CIRCUITSTATE/PBSEQ-D1/Export/R0.1/[1] 12-05-2024/PCB/PBSEQ-D1-R0.1-F_Silkscreen.pdf

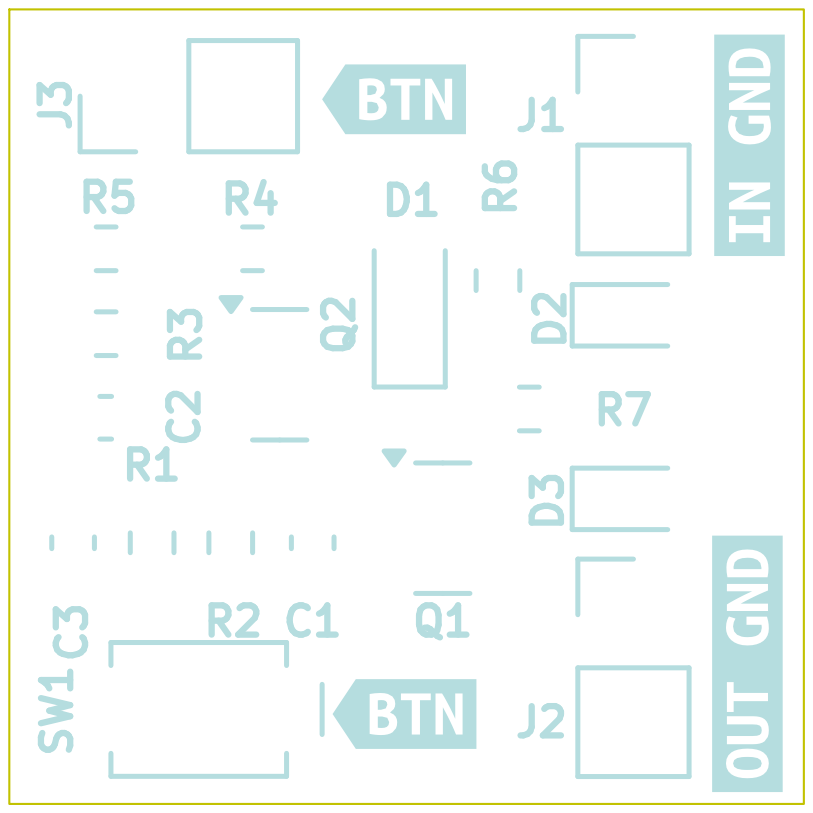
[picture p12: page 1]
