CIRCUITSTATE/PBSEQ-D1/Export/R0.1/[1] 12-05-2024/SCH/PBSEQ-D1-R0.1-SCH-12052024-1.pdf

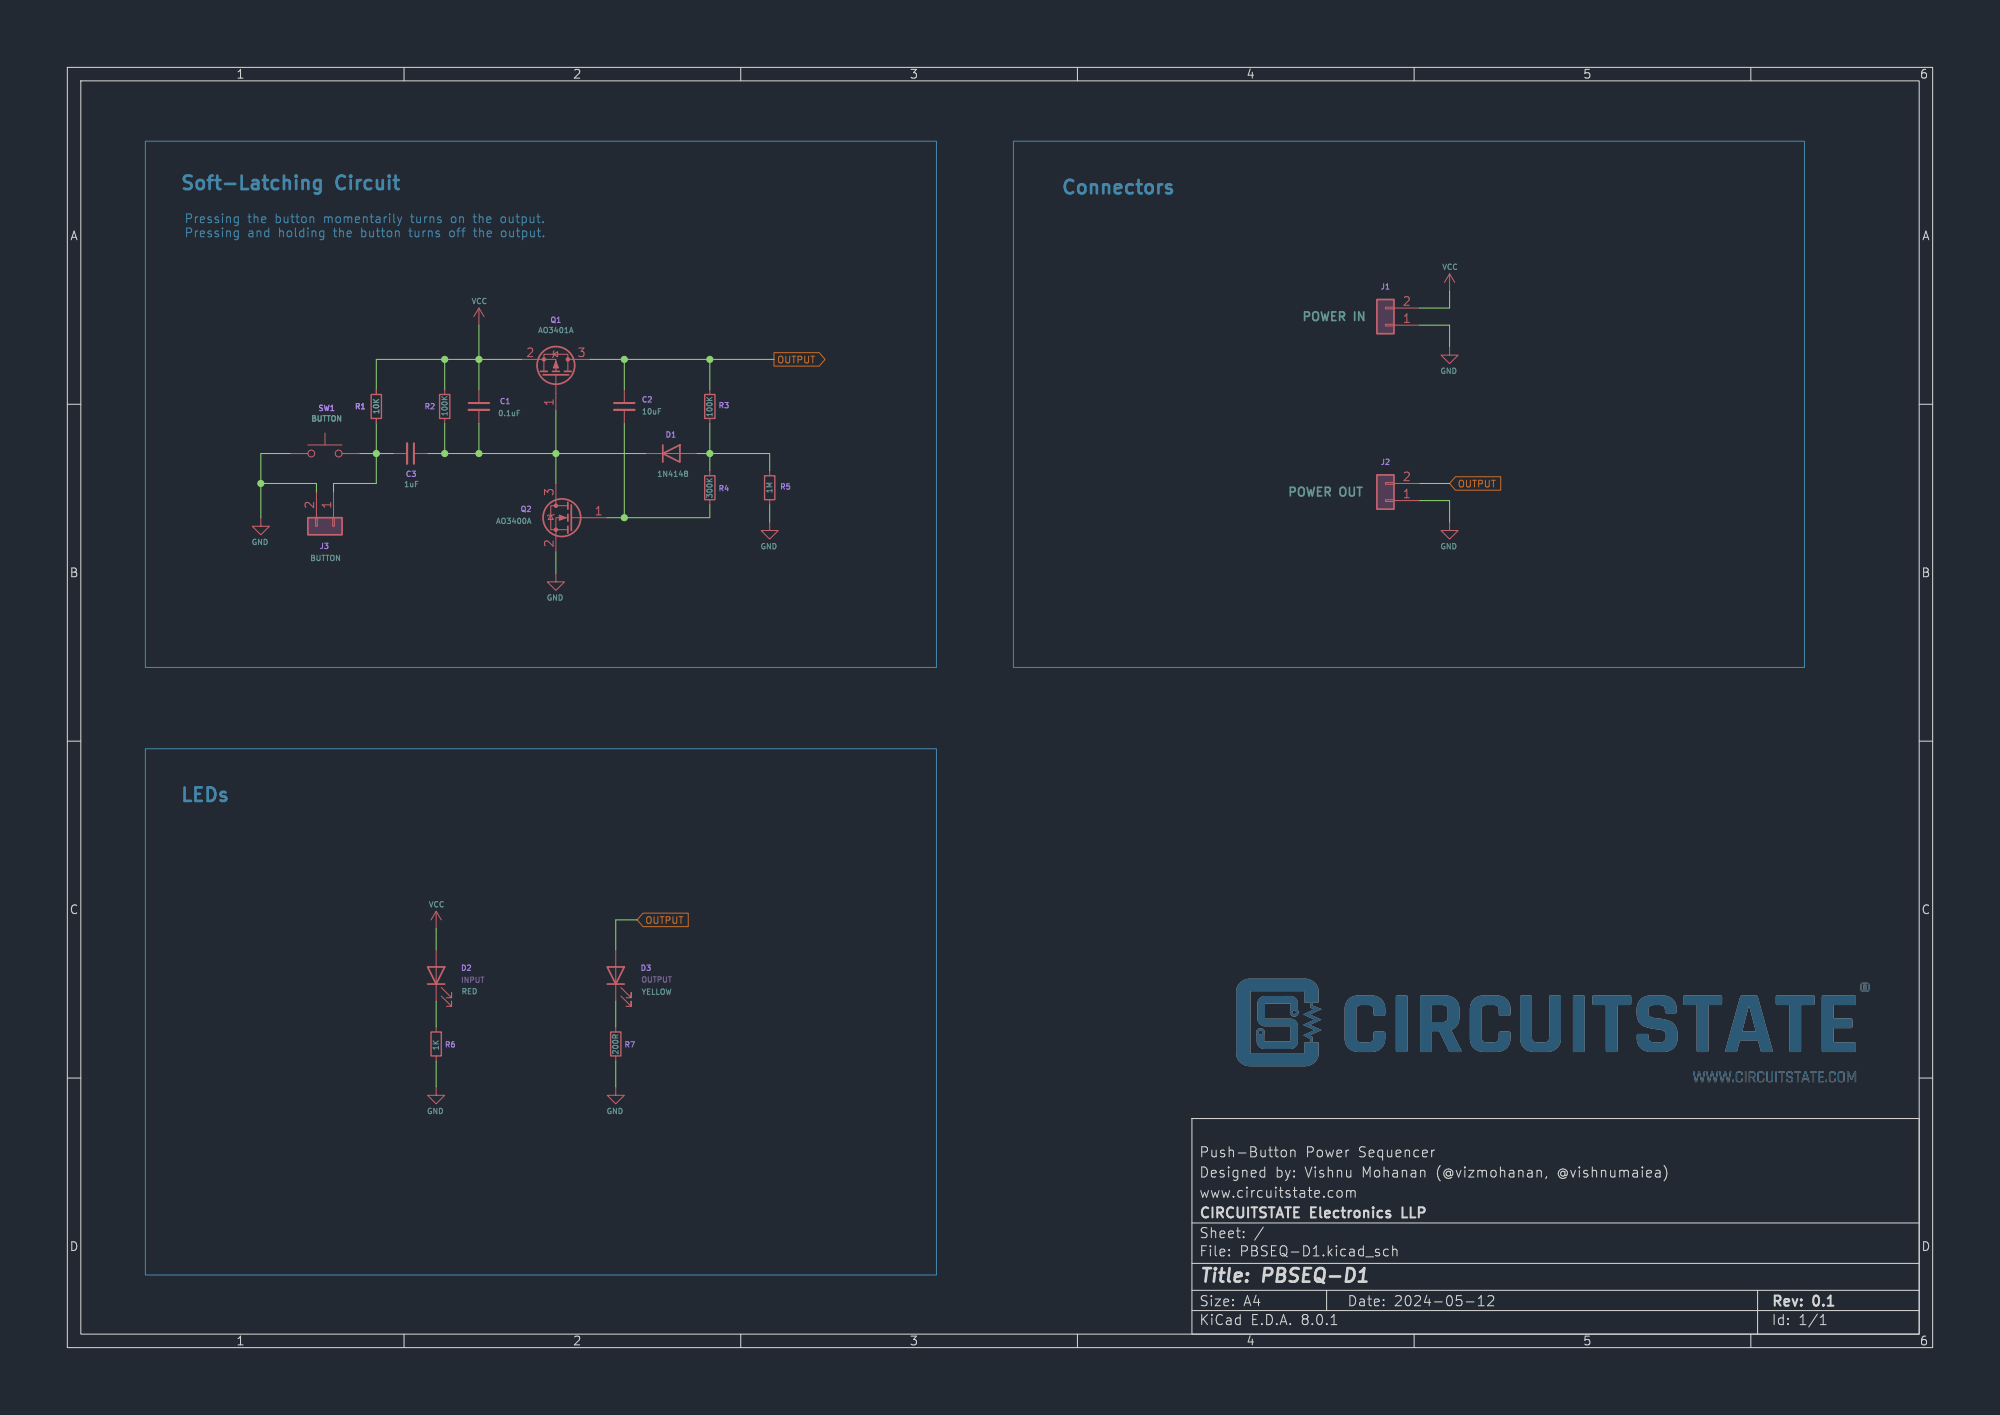
[picture p14: page 1]
